shufps/diy-projector-clock/images/22851997_1206666786132518_3949441219433421302_n.jpg

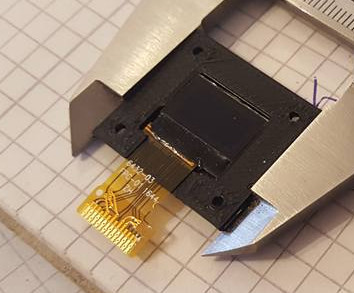
images/22851997_1206666786132518_3949441219433421302_n.jpg
