shufps/diy-projector-clock/images/22885966_1207940582671805_9052044658180000451_n.jpg

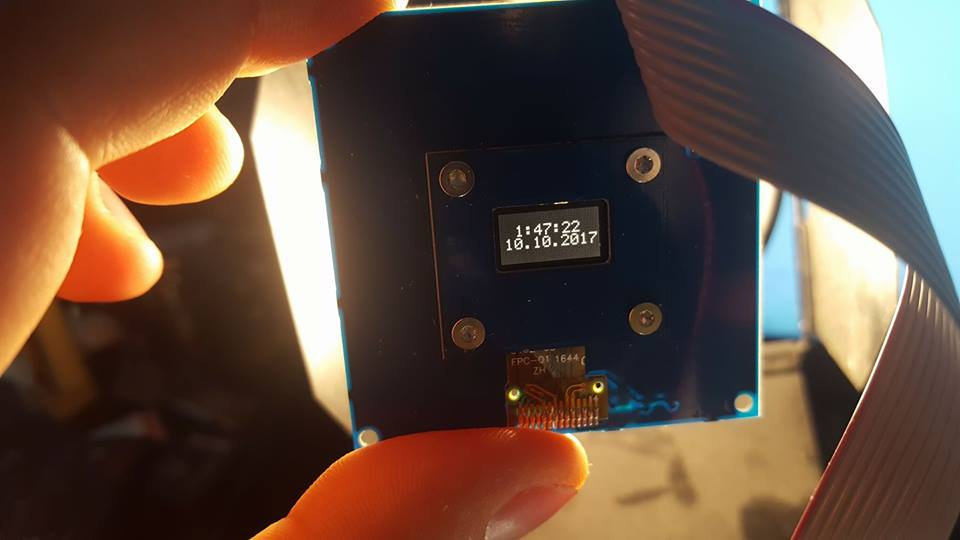
images/22885966_1207940582671805_9052044658180000451_n.jpg
