shufps/diy-projector-clock/images/23131607_1213188442147019_5008004252267984808_n.jpg

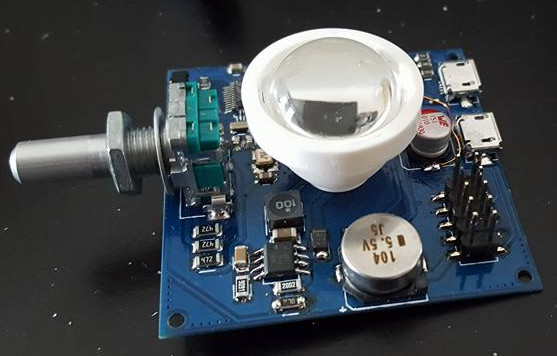
images/23131607_1213188442147019_5008004252267984808_n.jpg
