shufps/diy-projector-clock/images/23131890_1213188468813683_2381276653004583966_n.jpg

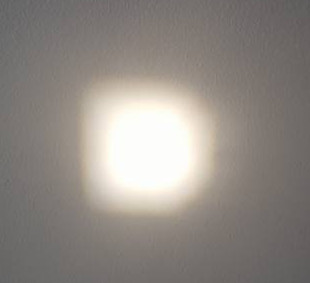
images/23131890_1213188468813683_2381276653004583966_n.jpg
