shufps/diy-projector-clock/images/23380218_1219804668152063_8622113328646516671_n.jpg

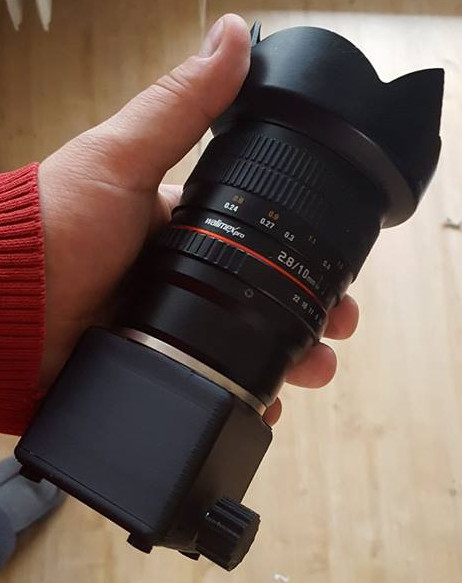
images/23380218_1219804668152063_8622113328646516671_n.jpg
