shufps/diy-projector-clock/images/23559460_1223772024421994_2585757183464992038_n.jpg

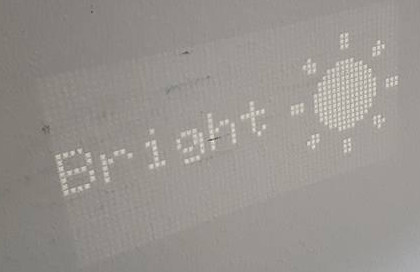
images/23559460_1223772024421994_2585757183464992038_n.jpg
