shufps/diy-projector-clock/images/23559568_1223771867755343_5931761190105667111_n.jpg

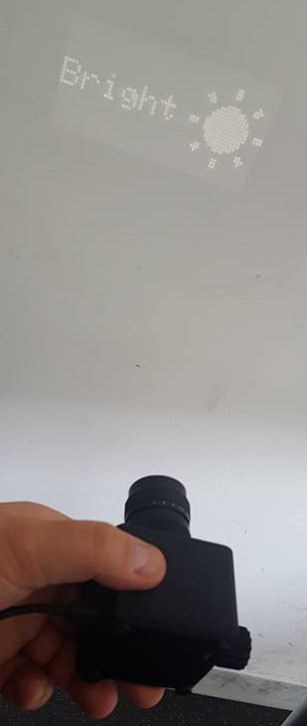
images/23559568_1223771867755343_5931761190105667111_n.jpg
