shufps/diy-projector-clock/images/DSC00244.JPG

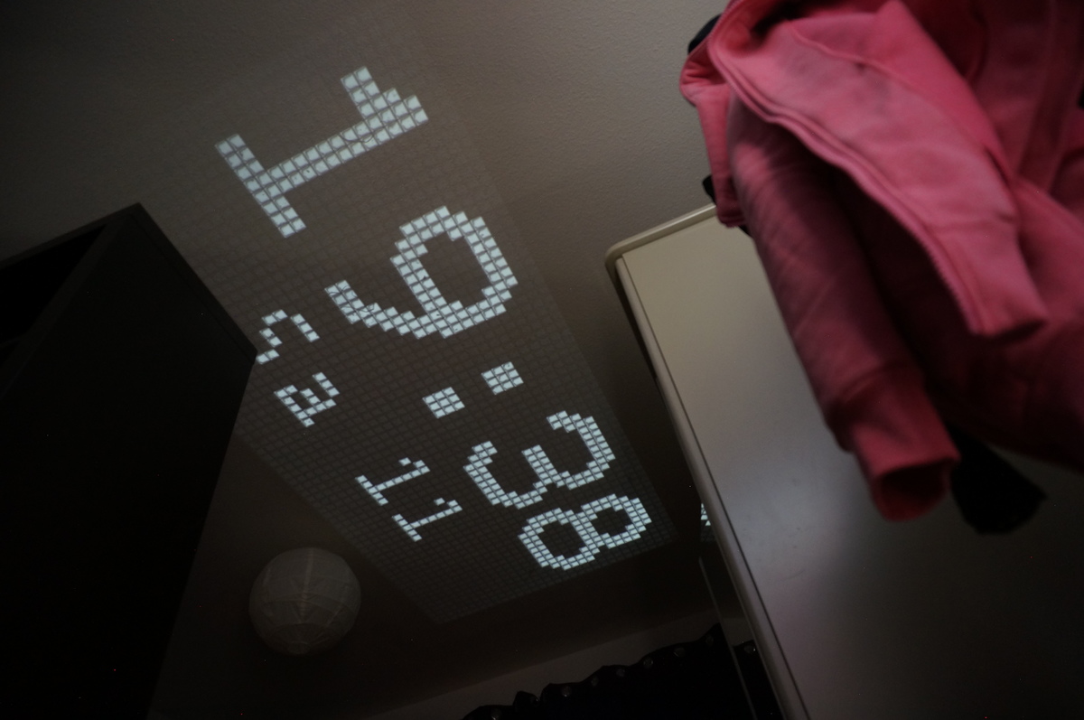
images/DSC00244.JPG
