shufps/diy-projector-clock/images/lcd.png

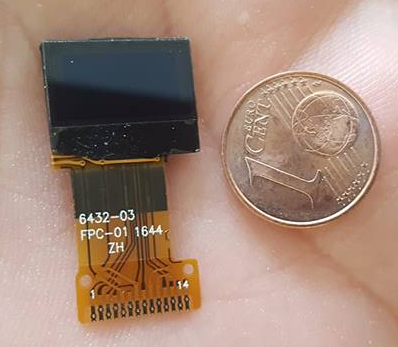
images/lcd.png
