shufps/diy-projector-clock/src/include/icons.h

/*
 * icons.h
 *
 *  Created on: 09.11.2017
 *      Author: ne23kaj2
 */

#ifndef ICONS_H_
#define ICONS_H_

/*
 * icons.c
 *
 *  Created on: 09.11.2017
 *      Author: ne23kaj2
 */

extern const char* icon_time;
extern const char* icon_date;
extern const char* icon_contrast;
extern const char* icon_brightness;
extern const char* icon_timer;
extern const char* icon_back;




#endif /* ICONS_H_ */
