shufps/diy-projector-clock/src/include/ir.h

#ifndef __IR_H__
#define __IR_H__

#include "main.h"
#include "irmp.h"


#define CMD_QUICK 0x17
#define CMD_FADE 0x07
#define CMD_SLOW 0x13
#define CMD_RED 0x58
#define CMD_GREEN 0x59
#define CMD_FLASH 0x0B
#define CMD_PLUS1 0x41
#define CMD_PLUS2 0x16
#define CMD_MINUS 0x12
#define CMD_SET 0x40
#define CMD_RPLUS 0x14
#define CMD_RMINUS 0x10
#define CMD_GPLUS 0x15
#define CMD_GMINUS 0x11


#endif
