shufps/diy-projector-clock/src/include/rotenc.h

/*
 * rotenc.h
 *
 *  Created on: 14.11.2017
 *      Author: ne23kaj2
 */

#ifndef ROTENC_H_
#define ROTENC_H_



void rotenc_irq_process();
void rotenc_init();
int8_t rotenc_read1(void);


#endif /* ROTENC_H_ */
