shufps/diy-projector-clock/src/include/ugui_config.h

#ifndef __UGUI_CONFIG_H
#define __UGUI_CONFIG_H

#include <stdint.h>

#ifdef __cplusplus
extern "C" {
#endif

/* -------------------------------------------------------------------------------- */
/* -- CONFIG SECTION                                                             -- */
/* -------------------------------------------------------------------------------- */

/* Enable needed fonts here */
//#define  USE_FONT_4X6
//#define  USE_FONT_5X8
//#define  USE_FONT_5X12
//#define  USE_FONT_6X8
#define  USE_FONT_6X10
//#define  USE_FONT_7X12
//#define  USE_FONT_8X8
//#define  USE_FONT_8X12
//#define  USE_FONT_8X14
//#define  USE_FONT_10X16
//#define  USE_FONT_12X16
//#define  USE_FONT_12X20
//#define  USE_FONT_16X26
//#define  USE_FONT_22X36
//#define  USE_FONT_24X40
//#define  USE_FONT_32X53

/* Specify platform-dependent integer types here */

#define __UG_FONT_DATA const
typedef uint8_t      UG_U8;
typedef int8_t       UG_S8;
typedef uint16_t     UG_U16;
typedef int16_t      UG_S16;
typedef uint32_t     UG_U32;
typedef int32_t      UG_S32;


/* -------------------------------------------------------------------------------- */
/* -------------------------------------------------------------------------------- */


/* Feature enablers */
#define USE_PRERENDER_EVENT
#define USE_POSTRENDER_EVENT

#ifdef __cplusplus
}
#endif

#endif
